ElectronicCats/CatSat/PDF's/14095953_1100317436683352_3034918497641182468_n.jpg

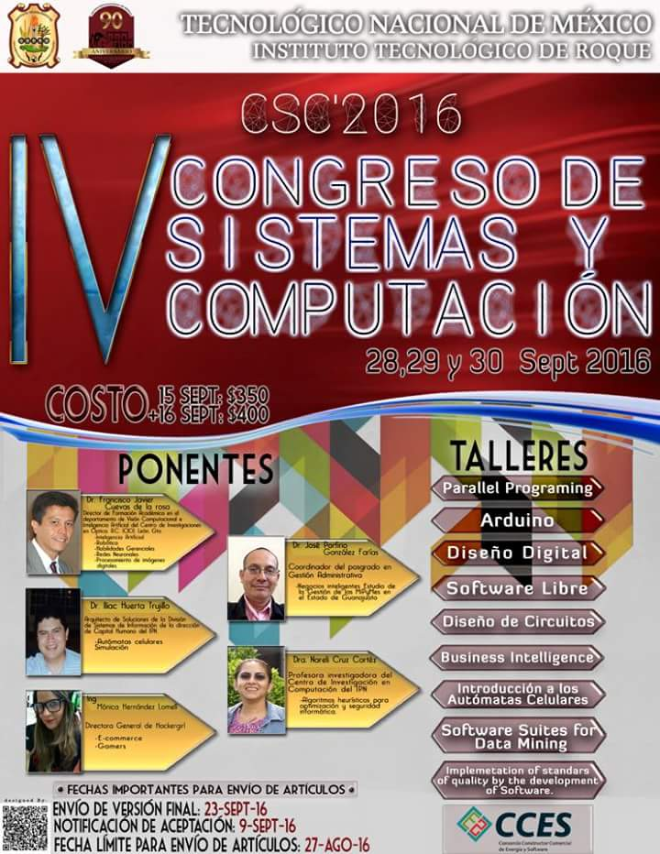
PDF's/14095953_1100317436683352_3034918497641182468_n.jpg
